MateusMaruzka/aqm_envcity_hw/simulations/power_path/powerpath_envcity.asc

I1: current; 500m
M1: pmos; FDR840P
M2: pmos; Si4403DY
M3: pmos; Si4403DY
M4: pmos; Si4403DY
Q1: pnp; 2N2907
Q2: pnp; 2N2907
Q3: pnp; 2N2907
Q4: pnp; 2N2907
Q5: pnp; 2N2907
Q6: pnp; 2N2907
R1: res; 10k
R2: res; 10k
R4: res; 47k
R5: res; 10k
R6: res; 47k
R7: res; 10k
R8: res; 47k
R9: res; 10k
V1: voltage; 5; Rser=0.5
V2: battery; 4
V3: voltage; PULSE(0 9 0 100m 100m 0 200m 5); Rser=0
Named nets: 0, Vin2, Vout2, Vin1, Vbat, Vusb, Vsolar, Vdiode+, Vdiode-
;.meas Pin AVG V(Vin1)*-I(V3)
;.meas Pout AVG V(Vout2)*i
;.meas eff param Pout/Pin
;.step param i 10m 1 25m
.tran 500m
