MateusMaruzka/aqm_envcity_hw/simulations/boost_mt3608/boost_mt3608.asc

C1: cap; 4.7µ
C2: cap; 10p
D1: schottky; RB10L-40
L1: ind; 1µ
R1: res; 113k
R2: res; 30k
R3: res; 500
U1: LT1930
V1: voltage; 3.3
Named nets: 0
.tran 1m
