MateusMaruzka/aqm_envcity_hw/simulations/mosfet as relay/mosfet_as_relay.asc

M1: pmos
Q1: npn
R1: res; 1k
R2: res; 1k
R3: res; 1k
R4: res; 100
R5: res; 2k
U1: LT1721
V1: voltage; 5
V2: voltage; 1
V3: voltage; 3.3
Named nets: 0, Vout, Vsignal, Vcc, Vin, Vin2, vin
.tran 10m
