MateusMaruzka/aqm_envcity_hw/simulations/power_path/power_path_heltec.asc

D1: schottky; 1N5817
D2: schottky; 1N5817
D3: diode; 1N914
I1: load; {i2}
M1: pmos; FDR840P
R1: res; 1k
S1: sw
S2: sw
V1: voltage; 0; Rser=0
V2: voltage; 5
V3: battery; 3
Named nets: 0, Vusb, Vpainel, Vusb_swo, Vpainel_swo, Vout2
Vantagem: circuito simples, painel e a fonte podem funcionar em conjunto;
Desvantagem: Tensão dissipada em cima dos diodos é por volta de 500mV
* Add um diodo entre a bateria e o dreno do mosfet
Vdiodo
.meas Pin2 AVG V(Vpainel)*-I(V2)
.meas Pout2 AVG V(Vout2)*I(I1)
.measn Eff2 param Pout2/Pin2
.step param i2 100m 1 100m
