MateusMaruzka/aqm_envcity_hw/simulations/power_path/power_path_heltec_2.asc

D1: schottky; 1N5817
D2: schottky; 1N5817
D3: diode; 1N914
I1: load; 500m
M1: pmos; FDR840P
R1: res; 1k
S1: sw
S2: sw
V1: voltage; 4.5; Rser=0
V2: voltage; 4.75
V3: battery; 4
Named nets: 0, Vusb, Vpainel, Vusb_swo, Vpainel_swo, Vout2
Vantagem: circuito simples, painel e a fonte podem funcionar em conjunto;
Desvantagem: Tensão dissipada em cima dos diodos é por volta de 500mV
Vdiodo
.meas Pin2 AVG V(Vpainel)*-I(V2)
.meas Pout2 AVG V(Vout2)*I(I1)
.meas Eff2 param Pout2/Pin2
;.step param i2 100m 1 100m
.tran 0.1
.model SW sw()
