MateusMaruzka/aqm_envcity_hw/simulations/power_path/power_path_heltec_charger.asc

A1: inv; Vhigh=5 Vlow = 0
D1: schottky; 1N5817
D2: schottky; 1N5817
D3: schottky; 1N5817
D4: LED; QTLP690C
D5: TVSdiode; SMBJ24CA
D6: zener; MMBZ6V8ALY
D7: zener; 1N750
M1: pmos; FDR840P
M2: pmos; FDR840P
R1: res; 10k
R2: res; 1k
R3: res; 50k
R4: res; 2k
R5: res; 100
R6: res; 1k
R7: res; 1k
R8: res; 300
U1: LTC4065
V1: battery; 3; Rser=50m
V2: voltage; 5; Rser=1
V3: voltage; 5; Rser=0.7
V4: voltage; 5
Named nets: 0, Vout2, Vbat, Vexternal, Vbat_protected, Vusb, Vsolar, Vcc, Vref
;tran 10m
.tran 10m
