MateusMaruzka/aqm_envcity_hw/simulations/power_path/powerpath_heltec.asc

D1: schottky; 1N5817
I1: load; 500m
M1: pmos; FDR840P
R1: res; 1k
S2: sw
V1: voltage; 5; Rser=0
V3: battery; 3
Named nets: 0, Vusb, Vusb_swo, Vout2, Vbat
Vdiodo
.tran 0.1
.model sw sw()
.step param i2 100m 1 100m
.meas Pin2 AVG V(Vusb)*-I(V1)
.meas Pbat AVG -V(Vbat)*I(V3)
.meas Pout2 AVG V(Vout2)*I(I1)
.meas Eff2 param Pout2/Pbat
.op
.model SW sw()
