MateusMaruzka/aqm_envcity_hw/simulations/power_path/single_zvd.asc

D1: schottky; 1N5817
M1: pmos; Si4403DY
Q1: pnp; 2N2907
Q2: pnp; 2N2907
R1: res; 47k
R2: res; 10k
V1: voltage; 5; Rser=0
V2: voltage; {V}; Rser=1m
Named nets: 0, Vn
.op
.step param V 5.5 4.5 0.05
